SuperMechaCow/OpenCritter/gfx/evolutions_graphics.png

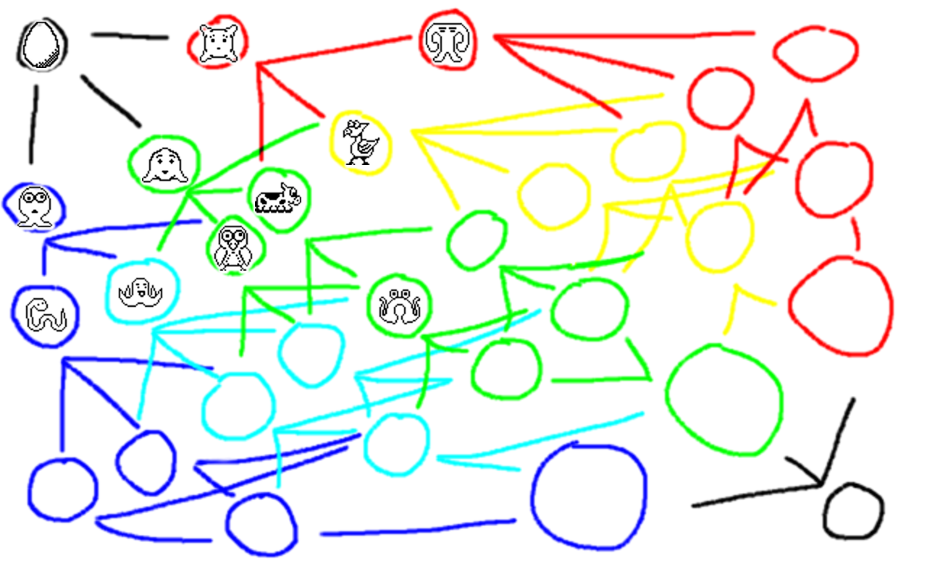
gfx/evolutions_graphics.png
