SuperMechaCow/OpenCritter/gfx/evolutions_params.png

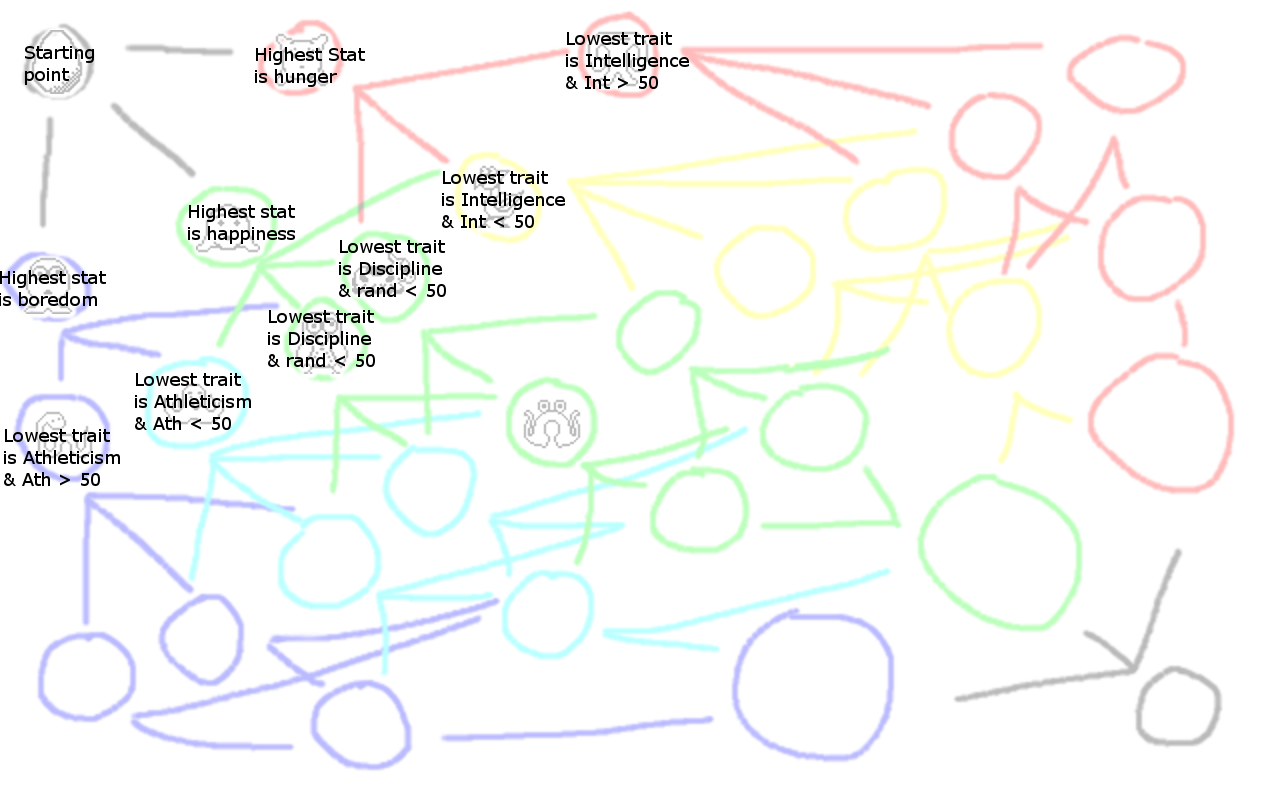
gfx/evolutions_params.png
