SuperMechaCow/OpenCritter/gfx/evolveposter.png

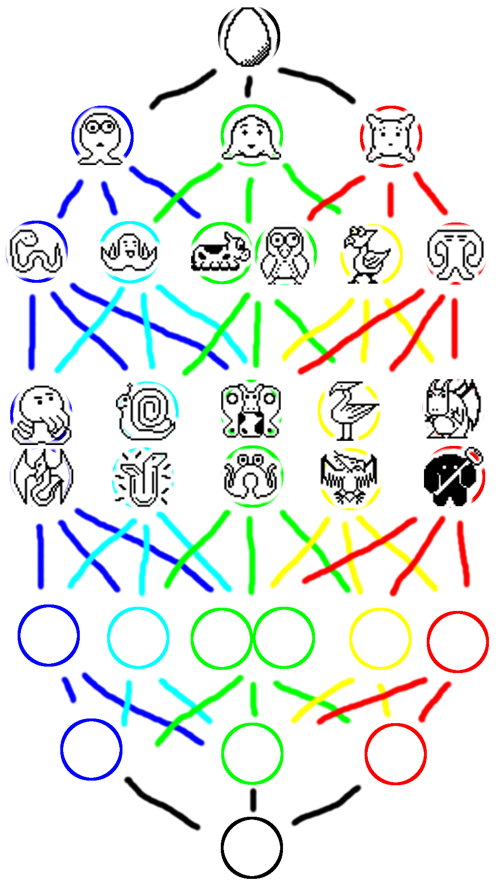
gfx/evolveposter.png
