SuperMechaCow/OpenCritter/gfx/media/IMG_20171023_132821901_HDR.jpg

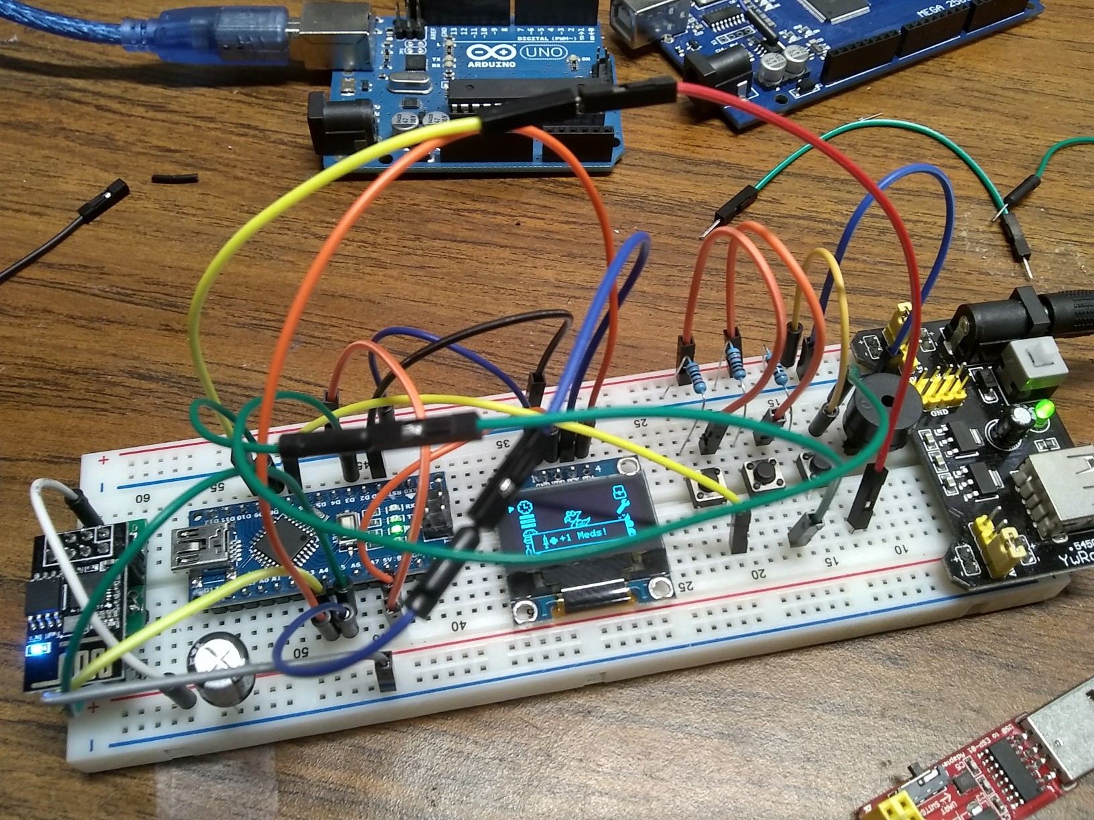
gfx/media/IMG_20171023_132821901_HDR.jpg
