SuperMechaCow/OpenCritter/reference/adafruit_characters.png

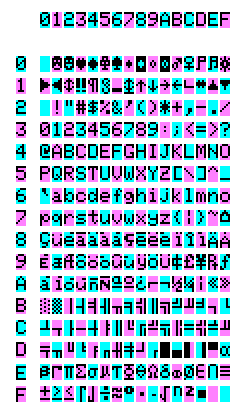
reference/adafruit_characters.png
