SuperMechaCow/OpenCritter/reference/attiny_web_by_pighixxx-d5u4aur.png

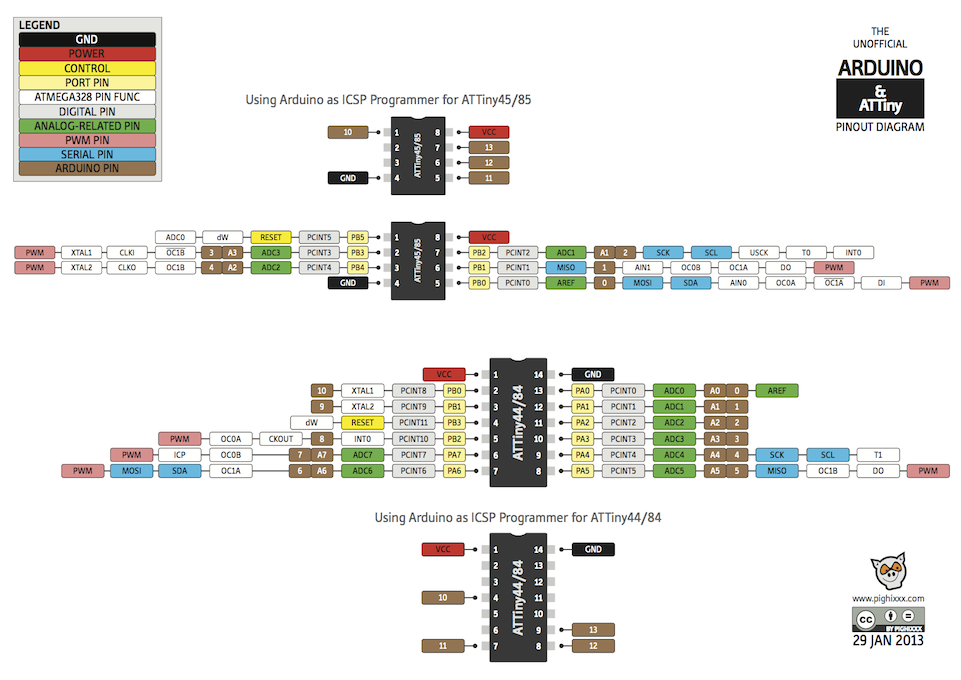
reference/attiny_web_by_pighixxx-d5u4aur.png
