SuperMechaCow/OpenCritter/reference/bot_preview.PNG

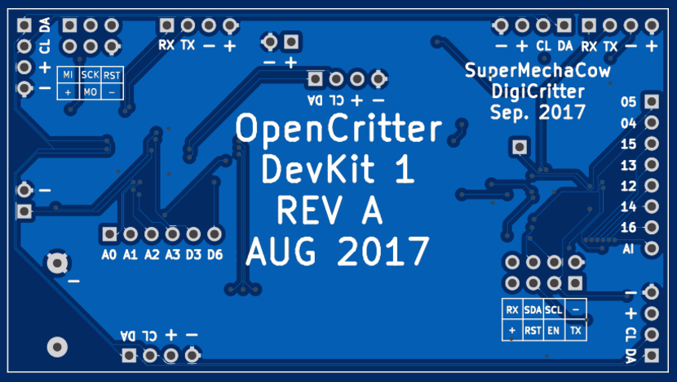
reference/bot_preview.PNG
