SuperMechaCow/OpenCritter/reference/esp8266ex-chip-pins.png

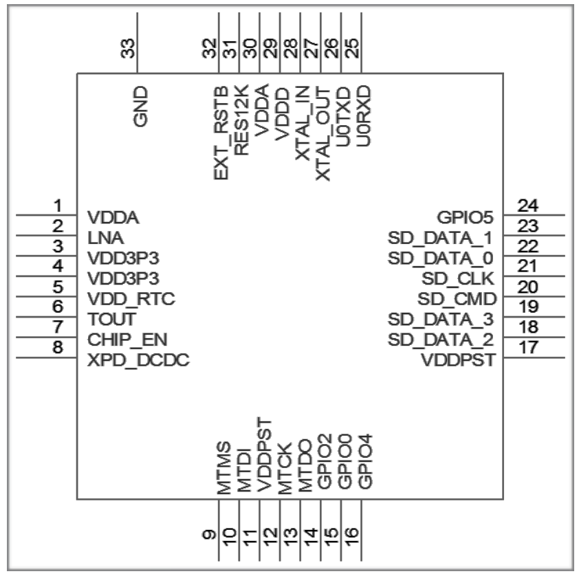
reference/esp8266ex-chip-pins.png
