SuperMechaCow/OpenCritter/reference/ESP-01_Schematic.png

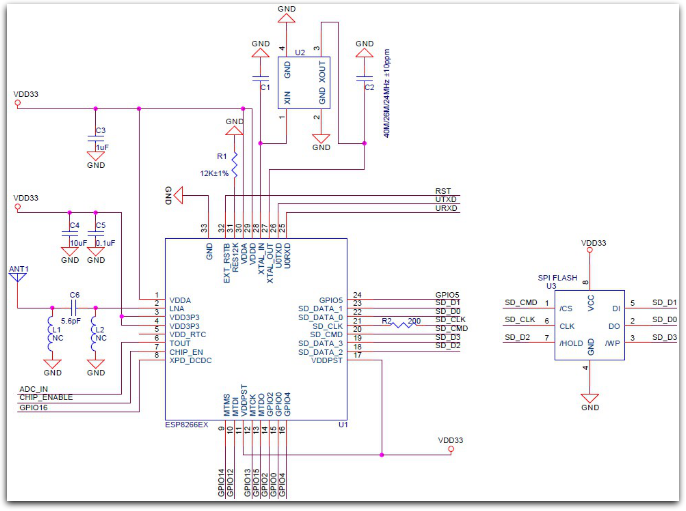
reference/ESP-01_Schematic.png
