SuperMechaCow/OpenCritter/reference/FTDI SERIAL.png

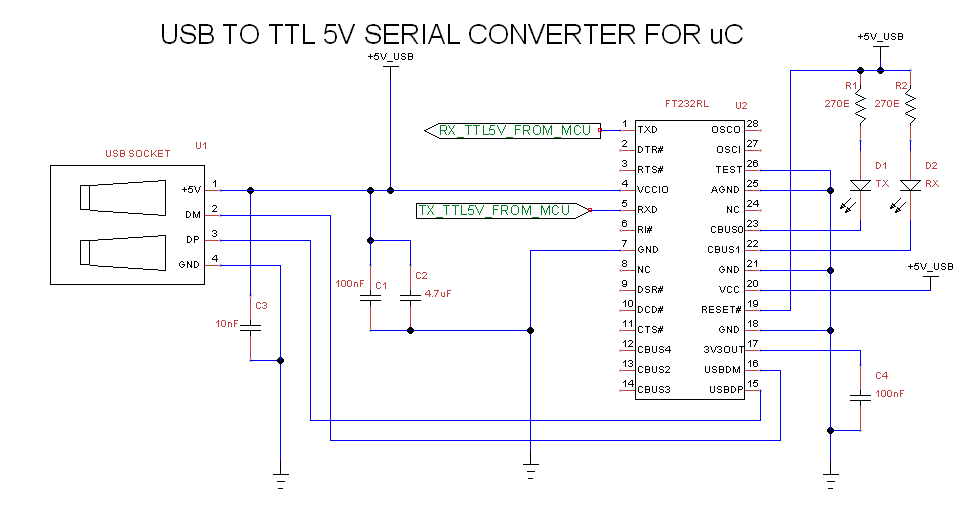
reference/FTDI SERIAL.png
