SuperMechaCow/OpenCritter/reference/ftdi_circuit.png

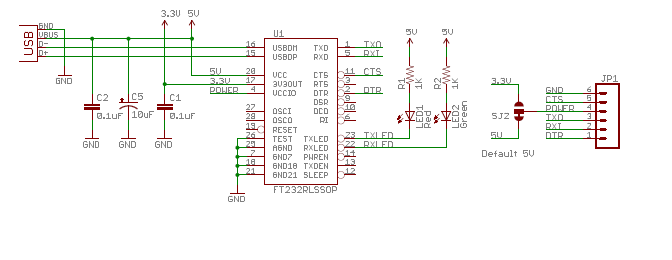
reference/ftdi_circuit.png
