SuperMechaCow/OpenCritter/reference/NodeMCU-to-Arduino-Pin-Mapping.png

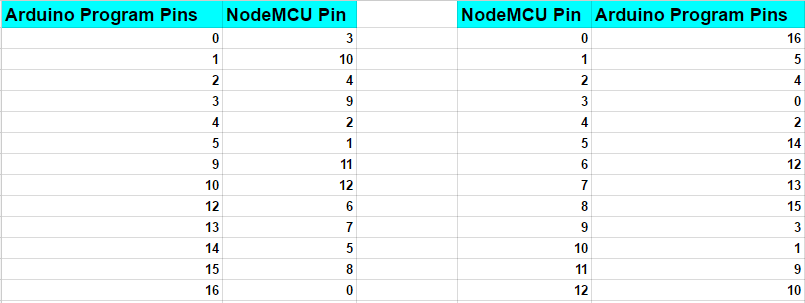
reference/NodeMCU-to-Arduino-Pin-Mapping.png
