SuperMechaCow/OpenCritter/reference/orchard-oled.png

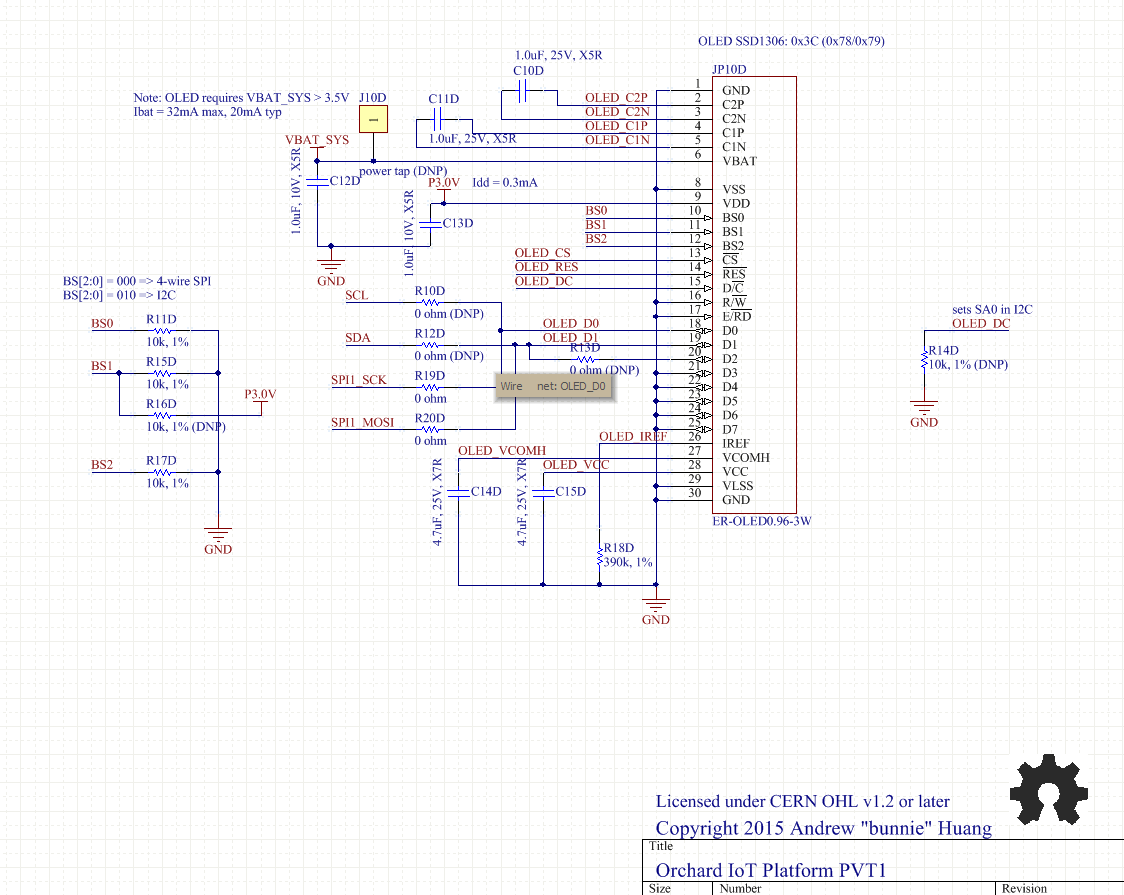
reference/orchard-oled.png
