SuperMechaCow/OpenCritter/reference/pgm-ftdi-basic-funduino-sch_l.png

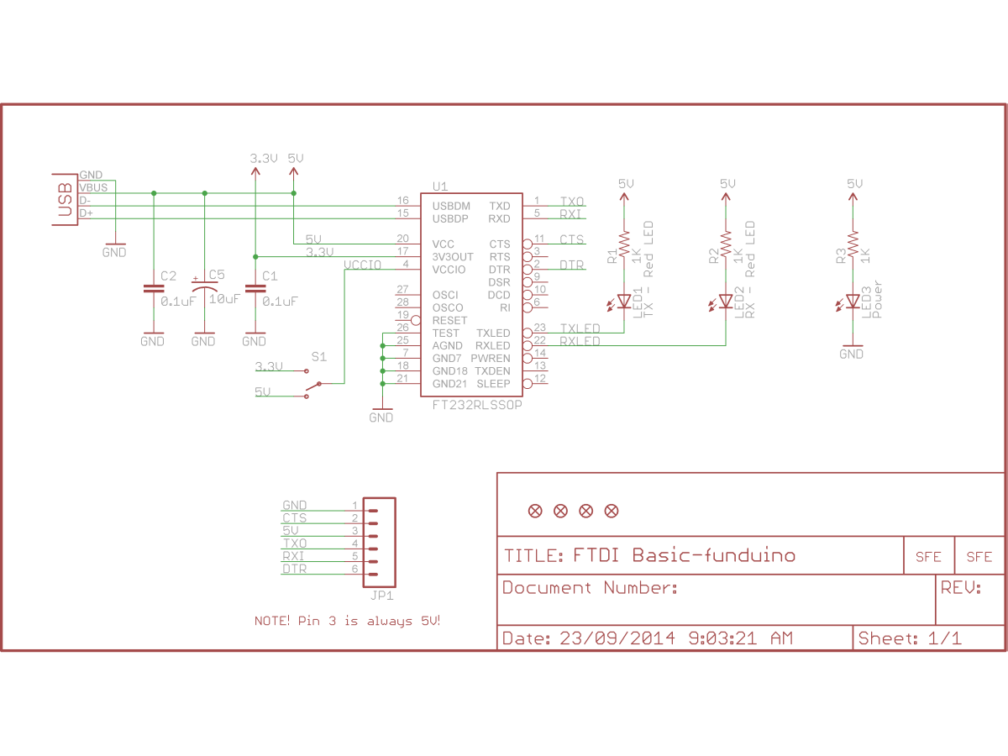
reference/pgm-ftdi-basic-funduino-sch_l.png
