SuperMechaCow/OpenCritter/reference/schematic.jpg

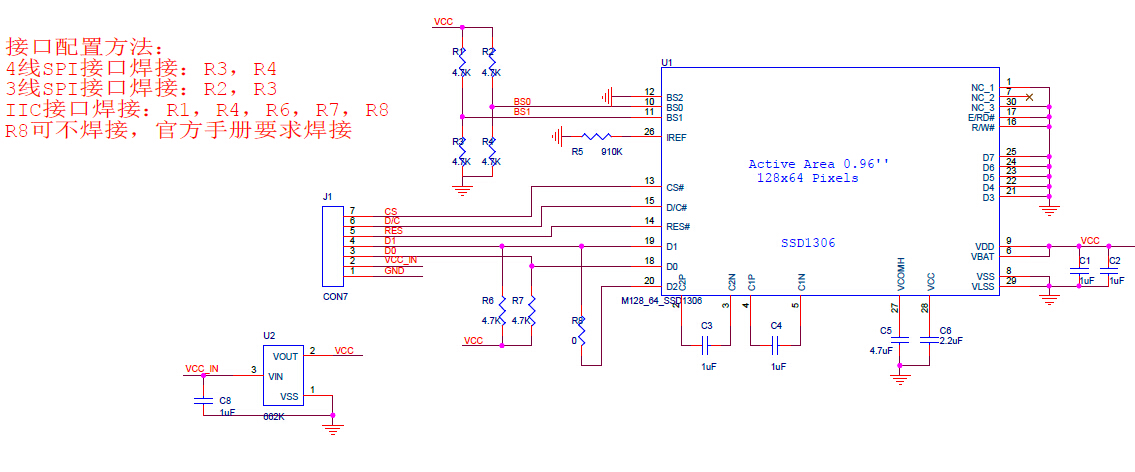
reference/schematic.jpg
