SuperMechaCow/OpenCritter/reference/top_preview.PNG

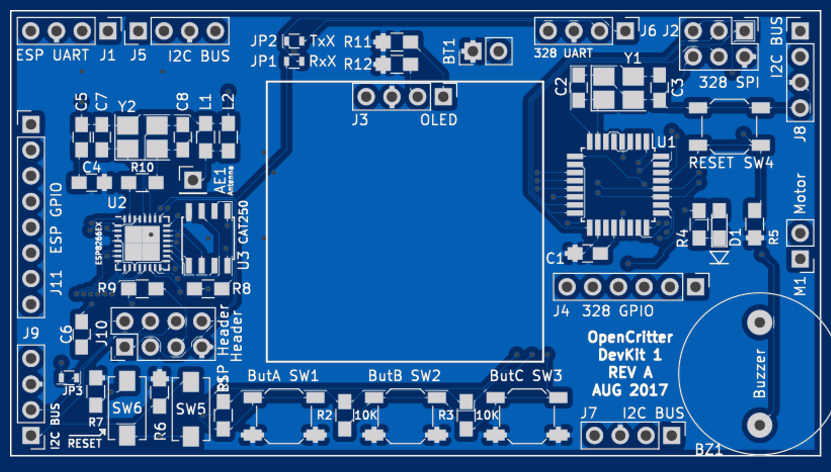
reference/top_preview.PNG
