SuperMechaCow/OpenCritter/software/opencritter_iopu_tiny/B_boardselect.h

//#ifdef __AVR_ATmega328P__
// IO Pins
#define hrt_pin           3
#define Abut_pin          0
#define Bbut_pin          1
#define Cbut_pin          2
#define buzzer_pin        8
#define beeper_pin        7
//Unused pins: 2, 4, 6 (11, 12, 13 for SPI)
// i2c and uart comms
#define i2c_addr          IOPU_Atmega328
#define serialbaud        115200
//#endif
