SuperMechaCow/OpenCritter/software/opencritter_main/C_setup.h

#define versionnum "a0.0013"
#define branchnum "0.00"
#define release "102417"

//Setup Access Point
const char *ssid = "OpenCritter";
const char *password = "Wibbur77";
//Start the server
ESP8266WebServer server(80);

//Start OLED
#define OLED_RESET 4
Adafruit_SSD1306 display(OLED_RESET);
#if (SSD1306_LCDHEIGHT != 64)
#error("Height incorrect, please fix Adafruit_SSD1306.h!");
#endif

// WiFi stuff
bool wifiEnabled = false;

// i2c module handler
bool IOPUattached = false;
bool GPUattached = false;
byte IOPUaddress = 10;
int i2c_devices[] = {0};

// Critter parameters
//Misc.
String crittername = "";
// Health Stats
byte Ath = 128;                 // Athleticism. How fast Hunger drains
byte Dis = 128;                 // Discipline. How fast happiness drains
byte Int = 128;                 // Intelligence. How fast Boredom drains
// Trait
byte hun = 255;                 // Hunger
byte hap = 255;                 // Happiness
byte bor = 255;                 // Boredom
// Energy Stats
byte Energy = 0;                // How much Energy the critter has to complete tasks
byte metabolism = 50;           // The frequency at which heartbeats occur
byte weight = 10;               // How much the critter "weighs"

// Bio-functions
bool deadcritter = false;
unsigned int heartbeats = 0;    // How many heartbeats have been... beaten?
unsigned int distressbeats = 0; // How many beats was the critter crying for attention?
float hrtBPM = 0;               // Beats per minute. Not vital to the game. Good for the user's imagination, though.
byte metaBonus = 0;             // A flat modifier of the metabolism from lifestage and medicines, etc.
byte lifestage = 0;             // What stage
int sick_thresh = 0;            // Roll for sickness on a sickness heartbeat if average health stats are under this number
int sick_thresh_bonus = 0;      // An additive modifier to the sick threshold
int queueBeats = 0;             // How many beats are we waiting to roll on?
byte poopCount = 0;             // How many poops are on the floor
byte sickCount = 0;             // What stage of sickness the critter is at
int sickRolls = 0;              // How many times was the critter left vulnerable to sickness?
bool Alert = false;             // Does the critter want/need attention?
byte breed = 0;                 // What breed in the breed index (see _labels.h) the critter is

// Heartbeat Events (Keyframe)
byte beat_health = 20;          // 10 //Roll to drain health every X heartbeats
byte beat_sick = 100;           //Roll for sickness every X heartbeats
byte beat_poop = 100;           //Roll for poop every X beats
byte beat_cry = 100;            //Roll to cry for attention every X heartbeats
int beat_hatch = 1000;          //How long it takes to hatch the egg
int beat_evolve = 10000;        //How many beats it takes to evolve
byte beat_energy = 20;          //How many beats before charging Energy

//Inventory Items
//A table of items with three properties. "total owned", "total acknowledged", and "max limit".
byte Inventory[inv_max_itemtypes][3] = {
  {inv_meds_start, inv_soda_start, inv_meds_max},     //meds
  {inv_soda_start, inv_soda_start, inv_soda_max},     //soda
  {inv_star_start, inv_star_start, inv_star_max},     //star
  {inv_biok_start, inv_biok_start, inv_biok_max},     //biok
  {inv_pedia_start, inv_pedia_start, inv_pedia_max},  //pedia
  {inv_labk_start, inv_labk_start, inv_labk_max}      //labk
};
unsigned int boostBeat = 0;     //When is the last heartbeat for the boost?
bool boostActive = false;

//Menu and cursor funtions
byte selMenu = 0;               // The currently selected menu
byte ocCursor = 0;              // The current position of the cursor

unsigned long CLK[8] = {0};     // The various clocks used in the game. See _labels.h for details

byte gfxBuffer[128] = {0};      // Used to store graphics for rendering on screen

/*========================================================================================================================*/

// OpenCritter supports 8 buttons, though it has 3 by default
bool butREAD[8] = {0};
bool butNOW[8] = {0};           // state of button to use
bool butTHEN[8] = {0};          // previous state of each button
//bool butREAD[8] = {0};          // State of the button received from IOPU
byte buttbyte = 0;

bool deviceSleep = false;

/*========================================================================================================================*/

//Animation functions
byte aniMode = 0;               // Which animation is currently playing?
byte aniOffset = 0;             // Offset the frames of the animation by this much
byte aniStage = 0;              // Which frame of the animation is playing?
byte aniLast = 0;               // What was the LAST frame to be played?
byte playPen_now = 48;          // The location of the critter on the main menu (playpen)
byte playPen_then = 48;         // The previous location of the critter in the playpen
byte foodType = 0;              // The type of food being eaten

//Real clock functions
int hnow, mnow, snow = 0; // Days, Hours, Minutes, Seconds right now
unsigned long clockOFFSET = 0;  // Offset the real clock by the game clokc by this much
bool hour12 = false;            // 'True' uses AM/PM system, 'False' uses 24 hour system

//Beeping functions
bool beepMute = false;          // Is the beeper muted?
byte beepMode = 0;              // Which beep are we playing?
byte beepOffset = 0;            // The pitch offset of the beep
byte beepStage = 0;             // What "frame" of the beeping are we currently on?

//Buzzing functions
bool rumbleMute = false;          // Is the rumble muted?
byte rumbleMode = 0;              // What type of rumble is playing?
byte rumbleStage = 0;             // What "frame" of the rumble are we currently on?

//Game functions
int gameStage = 0;              // What stage of each game we are on currently
int gameVal[10] = {0};          // Sets aside 10 integers to be re-used per game. See _labels.h for details
