SuperMechaCow/OpenCritter/software/opencritter_main/Z_gfx.h

/*
   This is just storage for image bitmaps.

   Atmega328 should have this page stored in external EEPROM and have code loaded for accessing it.
*/

static const unsigned char PROGMEM gfx_icon_food[] = {
  0x00, 0x00, 0x0F, 0xF0, 0x10, 0x08, 0x28, 0x24, 0x41, 0x02, 0x40, 0x12, 0x7F, 0xFE, 0x20, 0x04, 0x1F, 0x04, 0x20, 0xF8, 0x20, 0x04, 0x7F, 0xFE, 0x40, 0x02, 0x20, 0x04, 0x1F, 0xF8, 0x00, 0x00
};

static const unsigned char PROGMEM gfx_icon_clok[] = {
  0x00, 0x00, 0x07, 0xE0, 0x08, 0x90, 0x10, 0x08, 0x29, 0x14, 0x41, 0x02, 0x41, 0x02, 0x61, 0x06, 0x41, 0xE2, 0x40, 0x02, 0x40, 0x02, 0x28, 0x14, 0x10, 0x08, 0x08, 0x90, 0x07, 0xE0, 0x00, 0x00
};

static const unsigned char PROGMEM gfx_icon_stat[] = {
  0x00, 0x00, 0x7F, 0xFE, 0x7F, 0xFE, 0x7F, 0xFE, 0x00, 0x00, 0x00, 0x00, 0x7F, 0xFE, 0x7C, 0x02, 0x7F, 0xFE, 0x00, 0x00, 0x00, 0x00, 0x7F, 0xFE, 0x7F, 0xE2, 0x7F, 0xFE, 0x00, 0x00, 0x00, 0x00
};

static const unsigned char PROGMEM gfx_icon_game[] = {
  0x00, 0x00, 0x38, 0x00, 0x10, 0x1C, 0x10, 0x22, 0x10, 0x22, 0x28, 0x22, 0x44, 0x1C, 0x44, 0x00, 0x44, 0x08, 0x44, 0x1C, 0x44, 0x3E, 0x44, 0x08, 0x44, 0x10, 0x44, 0xE0, 0x38, 0x00, 0x00, 0x00
};

static const unsigned char PROGMEM gfx_icon_meds[] = {
  0x00, 0x00, 0x10, 0x00, 0x10, 0x00, 0x10, 0x00, 0x38, 0x00, 0x28, 0x38, 0x28, 0x38, 0x28, 0xFE, 0x28, 0xFE, 0x28, 0xFE, 0x7C, 0x38, 0x10, 0x38, 0x10, 0x00, 0x10, 0x00, 0x38, 0x00, 0x00, 0x00
};

static const unsigned char PROGMEM gfx_icon_conf[] = {
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
0x0C, 0x50, 0x85, 0x00, 0x06, 0x50, 0x85, 0x0C, 0x00, 0x50, 0x85, 0x18, 0x00, 0x50, 0x85, 0x30,
0x00, 0x40, 0x01, 0x00, 0x00, 0x40, 0x01, 0x00, 0x1C, 0x28, 0x0A, 0x20, 0x70, 0x24, 0x12, 0x30,
0x00, 0x13, 0xE4, 0x18, 0x00, 0x08, 0x08, 0x08, 0x00, 0x07, 0xF0, 0x00, 0x00, 0x00, 0x00, 0x00
};

static const unsigned char PROGMEM gfx_zeta_idle [] = {
0x00, 0x00, 0x00, 0x00, 0x30, 0x08, 0x10, 0x00, 0x18, 0x0C, 0x10, 0x38, 0x0C, 0x04, 0x30, 0xE0,
0x00, 0x00, 0x20, 0x00, 0x0F, 0xF0, 0x20, 0x00, 0x08, 0x08, 0x07, 0xF8, 0x09, 0xE4, 0x08, 0x08,
0x04, 0x12, 0x16, 0x08, 0x03, 0x09, 0x24, 0x10, 0x00, 0x84, 0xC0, 0x20, 0x30, 0x70, 0x80, 0x40,
0x18, 0x40, 0x80, 0x80, 0x0C, 0x50, 0x87, 0x0E, 0x00, 0x50, 0x81, 0x18, 0x00, 0x50, 0x81, 0x70,
0x00, 0x50, 0x85, 0x00, 0x00, 0x50, 0x85, 0x00, 0x07, 0x50, 0x85, 0x00, 0x1C, 0x50, 0x85, 0x00,
0x00, 0x50, 0x85, 0x00, 0x00, 0x50, 0x85, 0x06, 0x00, 0x50, 0x85, 0x0C, 0x02, 0x50, 0x85, 0x18,
0x02, 0x40, 0x01, 0x00, 0x06, 0x40, 0x01, 0x00, 0x0C, 0x28, 0x0A, 0x00, 0x08, 0x24, 0x12, 0x70,
0x08, 0x13, 0xE4, 0x1C, 0x00, 0x08, 0x08, 0x00, 0x00, 0x07, 0xF0, 0x00, 0x00, 0x00, 0x00, 0x00
};
