SuperMechaCow/OpenCritter/software/iopu_debugbutton/D_debug.ino

//void debug()
//{
//  if (Serial.available())
//  {
//    switch (Serial.parseInt())
//    {
//      case 1:
//        Serial.println(F("Test which sound?"));
//        while (!Serial.available())
//        {
//        }
//        beepMode = Serial.parseInt();
//        break;
//      case 2:
//        Serial.println(F("Testing buzzer: "));
//        while (!Serial.available())
//        {
//        }
//        beepMode = Serial.parseInt();
//        break;
//      default:
//        break;
//    }
//  }
//}
