SuperMechaCow/OpenCritter/opencritter_code/names.h

/*        ARRAY NAMES         */
//Functions
#define RESET 0
//CLOCK NAMES
#define baseCLK 0 //Base clock
#define hrtCLK 1  //Heartbeat clock
#define timeCLK 2 //Generic clock
#define butCLK 3  //Button clock
#define aniCLK  4 //Animation clock
#define beepCLK 5 //beeper clock
#define buzzCLK 6 //beeper clock
#define cryCLK 7 //time between crying for attention
//beepER NAMES
#define UpChirp 1
#define DnChirp 2
#define HiLo1 3
#define HiLo3 4
#define PosBeep 5
#define NegBeep 6
//MENU NAMES
#define mainM 1
#define clockM 2
#define statsM 3
#define foodM 4
#define gameM 5
#define medsM 6
#define confM 7
//ANIMATION TYPES
#define a_idle 1
#define a_eat 2
#define a_run 3
//ANIMATION NAMES
#define ani_egg_idle 1
#define ani_wibbur_idle 2
#define ani_wibbur_eat 3
#define ani_tribbur_idle 4
#define ani_tribbur_eat 5
//BREED NAMES
#define egg 0
#define wibbur 1
#define tribbur 2
//BASE WEIGHT
#define egg_w 5
#define wibbur_w 10
#define tribbur_w 20
